cfavreau/Laser-Show-Shield/OLSD_V4/Software_V4B/OLSC_VS2005_OLSD_V3_3/OLSC_VS2005_OLSD/OLSD/trace.h

#include <stdio.h>
#include <string.h>


#ifndef __TRACE_H__
#define __TRACE_H__

void EnableTrace(bool enable);

bool TraceIsEnabled(void);

void OpenTraceFile();

void CloseTraceFile();

void Trace(const char *format, ...);

#endif // __TRACE_H__
