cfavreau/Laser-Show-Shield/OLSD_V4/Software_V4B/OLSD_Firmware_V4_1/OLSD_Firmware/test_frames.h

#include <avr/pgmspace.h> // Macros to allow data storage in program (flash) space

// ILDA 12k Test Frame
#define ILDA12K_POINT_COUNT 4938
unsigned char ILDA12K_IMAGE[ILDA12K_POINT_COUNT] PROGMEM = {32,178,255,191,0,0,33,168,255,175,33,158,255,175,33,148,255,159,33,138,255,143,33,128,255,143,33,118,255,127,33,108,255,111,33,98,255,111,33,88,255,95,33,78,255,79,33,68,255,79,33,58,255,63,32,48,255,63,254,224,33,38,255,47,33,28,255,47,33,18,255,31,33,8,255,15,33,0,255,15,33,0,255,15,33,0,255,15,33,0,255,15,33,0,255,15,33,0,255,15,33,0,255,15,33,0,255,15,33,0,248,0,33,0,237,15,33,0,228,0,33,0,218,0,33,0,208,0,33,0,198,0,33,0,188,0,33,0,168,1,33,0,148,1,33,0,128,1,33,0,108,1,33,0,88,2,33,0,68,2,33,0,58,2,33,0,48,2,33,0,38,2,33,0,28,2,33,0,18,3,33,0,8,2,33,0,0,0,33,0,0,0,33,0,0,0,33,0,0,0,33,0,0,0,33,0,0,0,33,0,0,0,33,0,0,0,33,8,0,0,33,18,0,16,33,28,0,32,33,38,0,32,33,48,0,48,33,58,0,48,33,68,0,64,33,88,0,80,33,108,0,96,33,128,0,128,33,148,0,144,33,168,0,160,33,188,0,176,33,198,0,192,33,208,0,208,33,218,0,224,33,228,0,224,33,238,0,224,33,248,0,240,33,255,0,240,33,255,0,240,33,255,0,240,33,255,0,240,33,255,0,240,33,255,0,240,33,255,0,240,33,255,0,240,33,255,8,242,33,255,18,243,33,255,28,242,33,255,38,242,33,255,48,242,33,255,58,242,33,255,68,242,33,255,88,242,33,255,108,241,33,255,128,241,33,255,148,241,33,255,168,241,33,255,188,240,33,255,198,240,33,255,208,240,33,255,218,240,33,255,228,240,33,255,237,255,33,255,248,240,33,255,255,255,33,255,255,255,33,255,255,255,33,255,255,255,33,255,255,255,33,255,255,255,33,255,255,255,33,255,255,255,33,248,255,255,33,238,255,239,33,228,255,239,33,218,255,239,33,208,255,223,33,198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

// Laser Media Test Frame
#define LASERMEDIA_POINT_COUNT 2102
unsigned char LASERMEDIA_IMAGE[LASERMEDIA_POINT_COUNT] PROGMEM= {32,0,255,31,0,0,33,0,255,31,33,0,255,31,32,0,255,31,254,224,33,0,255,31,33,0,255,31,33,0,255,31,33,0,255,31,33,0,255,31,33,0,255,31,33,0,255,31,33,0,255,31,33,9,255,63,33,18,255,79,33,27,255,127,33,36,255,175,33,45,255,191,33,54,255,223,33,64,255,15,33,73,255,47,33,82,255,79,33,91,255,127,33,100,255,159,33,109,255,191,33,118,255,223,33,128,255,15,33,128,255,15,33,128,255,15,33,128,255,15,33,128,255,15,33,128,255,15,33,128,255,15,33,128,255,15,33,128,255,15,33,118,246,221,33,109,237,187,33,100,228,152,33,91,219,118,33,82,210,68,33,73,201,34,33,64,192,0,33,54,182,221,33,45,173,187,33,36,164,169,33,27,155,119,33,18,146,68,33,9,137,50,33,0,128,16,33,0,128,16,33,0,128,16,33,0,128,16,33,0,128,16,33,0,128,16,33,0,128,16,33,0,128,16,33,0,128,16,33,0,118,29,33,0,109,27,33,0,100,25,33,0,91,22,33,0,82,20,33,0,73,18,33,0,64,16,33,0,54,29,33,0,45,27,33,0,36,25,33,0,27,23,33,0,18,20,33,0,9,18,33,0,0,16,33,0,0,16,33,0,0,16,33,0,0,16,33,0,0,16,33,0,0,16,33,0,0,16,33,0,0,16,33,0,0,16,33,9,0,48,33,18,0,64,33,27,0,112,33,36,0,160,33,45,0,176,33,54,0,208,33,64,0,0,33,73,0,32,33,82,0,64,33,91,0,112,33,100,0,144,33,109,0,176,33,118,0,208,33,128,0,0,33,128,0,0,33,128,0,0,33,128,0,0,33,128,0,0,33,128,0,0,33,128,0,0,33,128,0,0,33,128,0,0,33,137,9,34,33,146,18,68,33,155,27,103,33,164,36,137,33,173,45,187,33,182,54,221,33,192,64,0,33,201,73,34,33,210,82,68,33,219,91,102,33,228,100,137,33,237,109,187,33,246,118,221,33,255,128,224,33,255,12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
